kosl/esphome-fake-eastron-SDM630-with-CTs/deye-esphome.yaml

substitutions:
  name: energy-meter                                                    #name in ESPhome
  device_description: "Esphome component for Deye sun-12k-sg04lp3"   #Description in ESPhome
  modbus_controller_id: sg04lp3                                      #just a random name for the modbus controler
  device_type: sun12k                                                #all entities in Home Assistant will start with this text to help identify the entitys 

esphome:
  name: ${name}

esp32:
  board: esp32-s3-fh4r2 # ESP32-S3 zero board
  framework:
    type: esp-idf

# Enable logging
logger:

# Enable Home Assistant API
api:

ota:
  - platform: esphome

wifi:
  networks:
    - ssid: !secret wifi_eteradxa_ssid
      password: !secret wifi_password
    - ssid: !secret wifi_garaza_ssid
      password: !secret wifi_password
    - ssid: !secret wifi_ssid
      password: !secret wifi_password
  output_power: 8.5dB
  power_save_mode: none  # Better reliability over power saving  
  ap:
    ssid: ${name}

captive_portal:

uart:
  # GPIO7 - TX to RX of bottom RS485 module
  # GPIO9 - RX to TX of bottom RS485 module
  - id: mod_bus
    tx_pin: GPIO1
    rx_pin: GPIO3
    baud_rate: 9600
    debug:
      direction: BOTH
 
modbus:
  id: modbus1
# flow_control_pin: 4 #for use when you use a rs485 board without auto flow control. Like the rs485 max board.
 
modbus_controller:
  - id: ${modbus_controller_id}
    address: 0x1
    modbus_id: modbus1
    setup_priority: -10
    update_interval: 15sec
  
switch:
  - platform: modbus_controller
    use_write_multiple: true
    modbus_controller_id: ${modbus_controller_id}
    name: ${device_type}_Solar_sell
    register_type: holding
    address: 145
    bitmask: 1
    entity_category: config
    icon: "mdi:toggle-switch"
 
  - platform: modbus_controller
    use_write_multiple: true
    modbus_controller_id: ${modbus_controller_id}
    name: ${device_type}-Grid_Charge
    register_type: holding
    address: 130
    bitmask: 1
    entity_category: config
    icon: "mdi:toggle-switch"
 
  - platform: modbus_controller
    use_write_multiple: true
    modbus_controller_id: ${modbus_controller_id}
    name: ${device_type}-Time of Use 
    id: ${device_type}_Time_of_Use
    register_type: holding
    address: 146
    bitmask: 1
    entity_category: config
    icon: "mdi:toggle-switch"
 
  - platform: modbus_controller  # Time point 1 charge enable - grid charging enable
    use_write_multiple: true
    modbus_controller_id: ${modbus_controller_id}
    name: ${device_type}-Time point 1 charge enable
    register_type: holding
    address: 172
    bitmask: 1   # 2 hvis man ønsker Gen charging enabel i sted for.
    entity_category: config
    icon: "mdi:toggle-switch"
 
  - platform: modbus_controller  # Time point 2 charge enable - grid charging enable
    use_write_multiple: true
    modbus_controller_id: ${modbus_controller_id}
    name: ${device_type}-Time point 2 charge enable
    register_type: holding
    address: 173
    bitmask: 1    # 2 hvis man ønsker Gen charging enabel i sted for.
    entity_category: config
    icon: "mdi:toggle-switch"
 
  - platform: modbus_controller  # Time point 3 charge enable - grid charging enable
    use_write_multiple: true
    modbus_controller_id: ${modbus_controller_id}
    name: ${device_type}-Time point 3 charge enable
    register_type: holding
    address: 174
    bitmask: 1    # 2 hvis man ønsker Gen charging enabel i sted for.
    entity_category: config
    icon: "mdi:toggle-switch"
 
  - platform: modbus_controller  # Time point 4 charge enable - grid charging enable
    use_write_multiple: true
    modbus_controller_id: ${modbus_controller_id}
    name: ${device_type}-Time point 4 charge enable
    register_type: holding
    address: 175
    bitmask: 1
    entity_category: config
    icon: "mdi:toggle-switch"
 
  - platform: modbus_controller  # Time point 5 charge enable - grid charging enable
    use_write_multiple: true
    modbus_controller_id: ${modbus_controller_id}
    name: ${device_type}-Time point 5 charge enable
    register_type: holding
    address: 176
    bitmask: 1
    entity_category: config
    icon: "mdi:toggle-switch"
 
  - platform: modbus_controller  # Time point 6 charge enable - grid charging enable
    use_write_multiple: true
    modbus_controller_id: ${modbus_controller_id}
    name: ${device_type}-Time point 6 charge enable
    register_type: holding
    address: 177
    bitmask: 1
    entity_category: config
    icon: "mdi:toggle-switch"
 
binary_sensor:
   - platform: modbus_controller
     modbus_controller_id: ${modbus_controller_id}
     skip_updates: 2
     name: ${device_type}-AC INV relay # bit 0
     id: ${device_type}_AC_INV_relay
     register_type: holding
     address: 552
     bitmask: 0x1
 
   - platform: modbus_controller
     modbus_controller_id: ${modbus_controller_id}
     skip_updates: 2
     name: ${device_type}-AC Load relay Reserved # bit 1
     id: ${device_type}_AC_Load_relay_Reserved
     register_type: holding
     address: 552
     bitmask: 0x2
 
   - platform: modbus_controller
     modbus_controller_id: ${modbus_controller_id}
     skip_updates: 2
     name: ${device_type}-AC grid relay # bit 2
     id: ${device_type}_AC_grid_relay
     register_type: holding
     address: 552
     bitmask: 0x4
 
   - platform: modbus_controller
     modbus_controller_id: ${modbus_controller_id}
     skip_updates: 2
     name: ${device_type}-AC Generator relay # bit 3
     id: ${device_type}_AC_Generator_relay
     register_type: holding
     address: 552
     bitmask: 0x8
 
   - platform: modbus_controller
     modbus_controller_id: ${modbus_controller_id}
     skip_updates: 2
     name: ${device_type}-Turn off/on status
     id: ${device_type}_Turn_off_on_status
     register_type: holding
     address: 551
     bitmask: 0x1
 
text_sensor:
   - platform: modbus_controller
     modbus_controller_id: ${modbus_controller_id}
     skip_updates: 2
     id: ${device_type}_Running_Status
     bitmask: 0
     register_type: holding
     address: 500
     raw_encode: HEXBYTES
     name: ${device_type}-Running Status
     lambda: |-
       uint16_t value = modbus_controller::word_from_hex_str(x, 0);
       switch (value) {
         case 0: return std::string("standby");
         case 1: return std::string("selfcheck");
         case 2: return std::string("normal");
         case 3: return std::string("alarm");
         case 4: return std::string("fault");
         default: return std::string("----");
       }
       return x;

number:
  - platform: modbus_controller
    use_write_multiple: true
    modbus_controller_id: ${modbus_controller_id}
    id: ${device_type}_Maximum_battery_charge_current
    name: "${device_type}-Maximum battery charge current"
    address: 108
    unit_of_measurement: A
    value_type: U_WORD
    
  - platform: modbus_controller
    use_write_multiple: true
    modbus_controller_id: ${modbus_controller_id}
    id: ${device_type}_Maximum_battery_discharge_current
    name: "${device_type}-Maximum battery discharge current"
    address: 109
    unit_of_measurement: A
    value_type: U_WORD

  - platform: modbus_controller
    use_write_multiple: true
    modbus_controller_id: ${modbus_controller_id}
    id: ${device_type}_Maximum_battery_grid_charge_current
    name: "${device_type}-Maximum battery_grid charge current"
    address: 128
    unit_of_measurement: A
    value_type: U_WORD

  - platform: modbus_controller
    use_write_multiple: true
    modbus_controller_id: ${modbus_controller_id}
    id: ${device_type}_max_solar_sell_power
    name: "${device_type}-Max Solar Sell Power"
    unit_of_measurement: W
    address: 143
    value_type: U_WORD

  - platform: modbus_controller
    use_write_multiple: true
    modbus_controller_id: ${modbus_controller_id}
    id: ${device_type}_Time_point_1
    name: "${device_type}-Time point 1 start"
    address: 148
    value_type: U_WORD
    
  - platform: modbus_controller
    use_write_multiple: true
    modbus_controller_id: ${modbus_controller_id}
    id: ${device_type}_Time_point_2
    name: "${device_type}-Time point 2 start"
    address: 149
    value_type: U_WORD
    
  - platform: modbus_controller
    use_write_multiple: true
    modbus_controller_id: ${modbus_controller_id}
    id: ${device_type}_Time_point_3
    name: "${device_type}-Time point 3 start"
    address: 150
    value_type: U_WORD
    
  - platform: modbus_controller
    use_write_multiple: true
    modbus_controller_id: ${modbus_controller_id}
    id: ${device_type}_Time_point_4
    name: "${device_type}-Time point 4 start"
    address: 151
    value_type: U_WORD
    
  - platform: modbus_controller
    use_write_multiple: true
    modbus_controller_id: ${modbus_controller_id}
    id: ${device_type}_Time_point_5
    name: "${device_type}-Time point 5 start"
    address: 152
    value_type: U_WORD
    
  - platform: modbus_controller
    use_write_multiple: true
    modbus_controller_id: ${modbus_controller_id}
    id: ${device_type}_Time_point_6
    name: "${device_type}-Time point 6 start"
    address: 153
    value_type: U_WORD
    
  - platform: modbus_controller
    use_write_multiple: true
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
    value_type: U_WORD
 
  - platform: modbus_controller
    modbus_controller_id: ${modbus_controller_id}
    name: "${device_type}-PV2 Current"
    id: ${device_type}_PV2_Current
    register_type: holding
    address: 679
    unit_of_measurement: "A"
    state_class: "measurement"
    accuracy_decimals: 1
    filters:
      - multiply: 0.1
    value_type: U_WORD  
 
  - platform: modbus_controller
    modbus_controller_id: ${modbus_controller_id}
    name: "${device_type}-Daily Production"
    id: ${device_type}_Daily_Production
    register_type: holding
    address: 529
    unit_of_measurement: "kWh"
    state_class: "total_increasing"
    device_class: energy
    accuracy_decimals: 1
    filters:
      - multiply: 0.1
    value_type: U_WORD  
 
  - platform: modbus_controller
    modbus_controller_id: ${modbus_controller_id}
    name: "${device_type}-Total PV Production"
    id: ${device_type}_Total_PV_Production
    register_type: holding
    address: 534
    skip_updates: 10
    unit_of_measurement: "kWh"
    state_class: "total_increasing"
    device_class: energy
    accuracy_decimals: 1
    value_type: U_DWORD_R
    filters:
      - multiply: 0.1
 
  - platform: modbus_controller
    modbus_controller_id: ${modbus_controller_id}
    name: "${device_type}-Total Grid Power"
    id: ${device_type}_Total_Grid_Power
    register_type: holding
    address: 625
    unit_of_measurement: "W"
    state_class: "measurement"
    accuracy_decimals: 0
    value_type: S_WORD
 
  - platform: modbus_controller
    modbus_controller_id: ${modbus_controller_id}
    skip_updates: 10
    name: "${device_type}-Daily Energy Bought"
    id: ${device_type}_Daily_Energy_Bought
    register_type: holding
    address: 520
    unit_of_measurement: "kWh"
    state_class: "total_increasing"
    device_class: energy
    accuracy_decimals: 1
    value_type: U_WORD
    filters:
      - multiply: 0.1
 
  - platform: modbus_controller
    modbus_controller_id: ${modbus_controller_id}
    skip_updates: 10
    name: "${device_type}-Daily Energy Sold"
    id: ${device_type}_Daily_Energy_Sold
    register_type: holding
    address: 521
    unit_of_measurement: "kWh"
    state_class: "total_increasing"
    device_class: energy
    accuracy_decimals: 1
    value_type: U_WORD
    filters:
      - multiply: 0.1
 
  - platform: modbus_controller
    modbus_controller_id: ${modbus_controller_id}
    skip_updates: 10
    name: "${device_type}-Total Energy Bought"
    id: ${device_type}_Total_Energy_Bought
    register_type: holding
    address: 522
    unit_of_measurement: "kWh"
    state_class: "total_increasing"
    device_class: energy
    accuracy_decimals: 1
    value_type: U_WORD
    filters:
      - multiply: 0.1
 
  - platform: modbus_controller
    modbus_controller_id: ${modbus_controller_id}
    skip_updates: 10
    name: "${device_type}-Total Energy Sold"
    id: ${device_type}_Total_Energy_Sold
    register_type: holding
    address: 524
    unit_of_measurement: "kWh"
    state_class: "total_increasing"
    device_class: energy
    accuracy_decimals: 1
    value_type: U_WORD
    filters:
      - multiply: 0.1
 
  - platform: modbus_controller #Total Consumption
    modbus_controller_id: ${modbus_controller_id}
    skip_updates: 10
    name: "${device_type}-Total Consumption"
    id: ${device_type}_Total_Consumption
    register_type: holding
    address: 527
    unit_of_measurement: "kWh"
    state_class: "total_increasing"
    device_class: energy
    accuracy_decimals: 2
    value_type: U_DWORD_R
    filters:
      - multiply: 0.1
 
  - platform: modbus_controller
    modbus_controller_id: ${modbus_controller_id}
    skip_updates: 10
    name: "${device_type}-active power generation of today"
    id: ${device_type}_active_power_generation_of_today
    register_type: holding
    address: 502
    unit_of_measurement: "kWh"
    state_class: "total_increasing"
    device_class: energy
    accuracy_decimals: 1
    value_type: S_WORD
    filters:
      - multiply: 0.1
 
  - platform: modbus_controller
    modbus_controller_id: ${modbus_controller_id}
    skip_updates: 2
    name: "${device_type}-Grid Current L1"
    id: ${device_type}_Grid_Current_L1
    register_type: holding
    address: 630
    unit_of_measurement: "A"
    state_class: "measurement"
    accuracy_decimals: 1
    filters:
      - multiply: 0.01
    value_type: S_WORD  
 
  - platform: modbus_controller
    modbus_controller_id: ${modbus_controller_id}
    skip_updates: 2
    name: "${device_type}-Grid Current L2"
    id: ${device_type}_Grid_Current_L2
    register_type: holding
    address: 631
    unit_of_measurement: "A"
    state_class: "measurement"
    accuracy_decimals: 1
    filters:
      - multiply: 0.01
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
    register_type: holding
    address: 518
    unit_of_measurement: "kWh"
    state_class: "total_increasing"
    device_class: energy
    accuracy_decimals: 1
    value_type: U_DWORD_R 
    filters:
      - multiply: 0.1
 
  - platform: modbus_controller
    modbus_controller_id: ${modbus_controller_id}
    name: "${device_type}-battery temperature"
    id:  ${device_type}_battery_temperature
    register_type: holding
    address: 586
    unit_of_measurement: "°C"
    accuracy_decimals: 1
    value_type: U_WORD 
    filters:
      - offset: -1000
      - multiply: 0.1
 
  - platform: modbus_controller
    modbus_controller_id: ${modbus_controller_id}
    name: "${device_type}-battery voltage"
    id: ${device_type}_battery_voltage
    register_type: holding
    address: 587  
    unit_of_measurement: "V"
    state_class: "measurement"
    accuracy_decimals: 2
    filters:
      - multiply: 0.01
    value_type: U_WORD
 
  - platform: modbus_controller
    modbus_controller_id: ${modbus_controller_id}
    skip_updates: 2
    name: "${device_type}-battery capacity"
    id: ${device_type}_battery_capacity
    register_type: holding
    address: 588
    unit_of_measurement: "%"
    state_class: "measurement"
    accuracy_decimals: 1
    value_type: U_WORD
 
  - platform: modbus_controller
    modbus_controller_id: ${modbus_controller_id}
    name: "${device_type}-Battery output power"
    id: ${device_type}_Battery_output_power
    register_type: holding
    address: 590
    unit_of_measurement: "W"
    state_class: "measurement"
    accuracy_decimals: 0
    value_type: S_WORD 
 
  - platform: modbus_controller
    modbus_controller_id: ${modbus_controller_id}
    name: "${device_type}-Battery output current"
    id: ${device_type}_Battery_output_current
    register_type: holding
    address: 591
    unit_of_measurement: "A"
    state_class: "measurement"
    accuracy_decimals: 2
    filters:
      - multiply: 0.01
    value_type: S_WORD
    
select:
  - platform: modbus_controller
    use_write_multiple: true
    modbus_controller_id: ${modbus_controller_id}
    name: ${device_type}-Energy priority
    address: 141
    value_type: U_WORD
    optionsmap:
      "Battery first": 0
      "Load first": 1

  - platform: modbus_controller
    use_write_multiple: true
    modbus_controller_id: ${modbus_controller_id}
    name: "${device_type}-Limit control mode"
    address: 142
    value_type: U_WORD
    optionsmap:
      "Selling first": 0
      "Zero export to load": 1
      "Zero export to CT": 2
